Clear492g/ClearWeatherClock/ESPArduino/WeatherStationFonts.h

/**The MIT License (MIT)

Copyright (c) 2015 by Daniel Eichhorn

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
See more at http://blog.squix.ch
*/
// Created by http://oleddisplay.squix.ch/ Consider a donation
// In case of problems make sure that you are using the font file with the correct version!
const uint8_t Meteocons_Plain_36[] PROGMEM = {
	0x25, // Width: 37
	0x26, // Height: 38
	0x20, // First Char: 32
	0xE0, // Numbers of Chars: 224

	// Jump Table:
	0xFF, 0xFF, 0x00, 0x24,  // 32:65535
	0x00, 0x00, 0xB6, 0x25,  // 33:0
	0x00, 0xB6, 0xB1, 0x24,  // 34:182
	0x01, 0x67, 0xB1, 0x24,  // 35:359
	0x02, 0x18, 0xB1, 0x24,  // 36:536
	0x02, 0xC9, 0xB3, 0x24,  // 37:713
	0x03, 0x7C, 0xB2, 0x24,  // 38:892
	0x04, 0x2E, 0x73, 0x24,  // 39:1070
	0x04, 0xA1, 0xB2, 0x24,  // 40:1185
	0x05, 0x53, 0x9F, 0x24,  // 41:1363
	0x05, 0xF2, 0x80, 0x24,  // 42:1522
	0x06, 0x72, 0x7F, 0x24,  // 43:1650
	0xFF, 0xFF, 0x00, 0x24,  // 44:65535
	0xFF, 0xFF, 0x00, 0x24,  // 45:65535
	0xFF, 0xFF, 0x00, 0x24,  // 46:65535
	0xFF, 0xFF, 0x00, 0x24,  // 47:65535
	0x06, 0xF1, 0xB2, 0x25,  // 48:1777
	0x07, 0xA3, 0xA3, 0x24,  // 49:1955
	0x08, 0x46, 0x80, 0x24,  // 50:2118
	0x08, 0xC6, 0xB3, 0x24,  // 51:2246
	0x09, 0x79, 0xB3, 0x24,  // 52:2425
	0x0A, 0x2C, 0xB2, 0x24,  // 53:2604
	0x0A, 0xDE, 0xB1, 0x24,  // 54:2782
	0x0B, 0x8F, 0xB2, 0x24,  // 55:2959
	0x0C, 0x41, 0xB1, 0x25,  // 56:3137
	0x0C, 0xF2, 0xB2, 0x24,  // 57:3314
	0xFF, 0xFF, 0x00, 0x24,  // 58:65535
	0xFF, 0xFF, 0x00, 0x24,  // 59:65535
	0xFF, 0xFF, 0x00, 0x24,  // 60:65535
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
};
